billism1/3d-print-cap-wall-mount/images/cap_mounts_with_caps_02 (1365x768).jpg

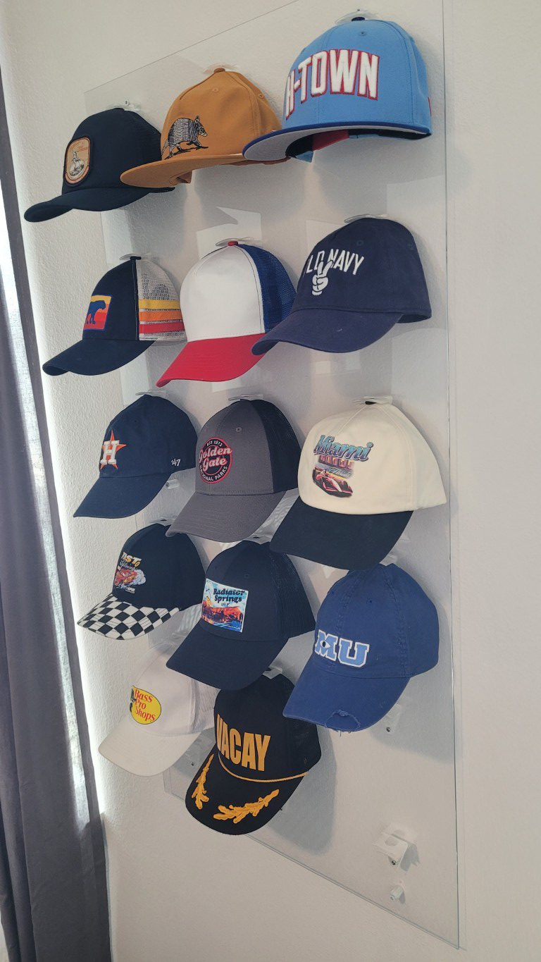
images/cap_mounts_with_caps_02 (1365x768).jpg
